kwan3217/Loginator/Yukari/config.cpp

#include "readconfig.h"
#include "config.h"

Config config;

const char* const ReadConfig::tagNames[]={
"GSENS",
"GODR",
"GBW",
"P",
"I",
"D",
"WP",
"THR",
"SCL",
"CCOUNT",
"CSPD",
"MANV",
"TCUT",
"TICK",
nullptr};

const ReadConfigEntry   ReadConfig::entries[]={
  {ReadConfig::typeInt,&config.gyroSens           ,nullptr           }, //GSENS
  {ReadConfig::typeInt,&config.gyroODR            ,nullptr           }, //GODR
  {ReadConfig::typeInt,&config.gyroBW             ,nullptr           }, //GBW
  {ReadConfig::typeFp ,&config.P                  ,nullptr           }, //P
  {ReadConfig::typeFp ,&config.I                  ,nullptr           }, //I
  {ReadConfig::typeFp ,&config.D                  ,nullptr           }, //D
  {ReadConfig::typeV2 , config.waypoint           ,&config.nWaypoints}, //WP
  {ReadConfig::typeInt,&config.throttle           ,nullptr           }, //THR
  {ReadConfig::typeV3 ,&config.gyroScl            ,nullptr           }, //SCL
  {ReadConfig::typeInt,&config.compassCountdownMax,nullptr           }, //CCOUNT
  {ReadConfig::typeFp ,&config.compassSpeed       ,nullptr           }, //CSPD
  {ReadConfig::typeFp ,&config.maneuverRate       ,nullptr           }, //MANV
  {ReadConfig::typeFp ,&config.tCutoff            ,nullptr           }, //TCUT
  {ReadConfig::typeFp ,&config.tickSize           ,nullptr           }, //TICK
};
