kwan3217/Loginator/Yukari/v3/sim/sim_Serial.cpp

/*
  HardwareSerial.cpp - Hardware serial library for Wiring
  Copyright (c) 2006 Nicholas Zambetti.  All right reserved.

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
  Modified 23 November 2006 by David A. Mellis
  Modified 28 September 2010 by Mark Sproul
*/

#include <stdlib.h>
#include <stdio.h>
#include <string.h>
#include <inttypes.h>
#include "Serial.h"
#include "robot.h"
#include "Time.h"

// Constructors ////////////////////////////////////////////////////////////////

HardwareSerial::HardwareSerial(int Lport):
#ifndef NOINT
txBuf(bufSize,txBuf_loc),rxBuf(bufSize,rxBuf_loc),
#endif
port(Lport) {

}

// Public Methods //////////////////////////////////////////////////////////////

void HardwareSerial::begin(unsigned int baud) {

}

void HardwareSerial::end() {

}

void HardwareSerial::write(uint8_t c) {
  ::printf("%c",c);
}

int HardwareSerial::available(void) {return state->hasGPS();}; //Returns 0 or 1 if none or some bytes are present
int HardwareSerial::peek(void) {return state->gpsBuf[state->gpsTransPointer];};                      //Not supported
int HardwareSerial::read(void) {
  char result=state->gpsBuf[state->gpsTransPointer];
  state->gpsTransPointer++;
  return result;
};
void HardwareSerial::flush(void) {}; //Enable FIFOs and reset both

// Preinstantiate Objects //////////////////////////////////////////////////////

HardwareSerial Serial(0);
HardwareSerial Serial1(1);
